cruz-control/sim-to-real/testing/jetson_servo/jetson_servo_PWM_test2.py

import Jetson.GPIO as GPIO
import time
GPIO.setmode(GPIO.BOARD)
channel = 33

GPIO.setup(channel, GPIO.OUT)

while True:
   GPIO.output(channel, GPIO.HIGH)
   
   time.sleep(1)
   GPIO.output(channel, GPIO.LOW)

   time.sleep(1)

GPIO.cleanup()
